kandonie/mqp/src/Firmware/ACC_Firmware/src/movement.h

void movementSetup();
void setPIDGains(double proportional, double integral, double derivative);
void testPWM();
void enablePWM(String system);
void disablePWM(String system);
void setRight(int speed);
void setLeft(int speed);
void setWeapon(int speed);
boolean PWMDriveDisabled();
boolean PWMWeaponDisabled();
bool turnToAngle(double currentHeading, double desiredHeading);
bool driveDistance(int encoderTicks, double distGoal);
void estopRobot();
