kandonie/mqp/src/Robot_Locomotion/MotorEnums.py

from enum import Enum


class PWMVals(Enum):
    ## CW/CCW refers to motor rotation
    FULL_CW = "2000"
    FULL_CCW = "1000"
    STOPPED = "1500"

class PIDVals(Enum):
    KP_DEFAULT = "0"
    KI_DEFAULT = "0"
    KD_DEFAULT = "0"

class MovementVals(Enum):
    HEADING_DEFAULT = "0"
    DISTANCE_DEFAULT = "0"
